wsular/urbanova-aqnet-rpi-node/testing/20161214_rooftest/SOAK2-PM10_004.csv

Instrument Name | DustTrak II
Model Number | 8530
Serial Number | 8530150710
Firmware Version | 3.4
Calibration Date | 2015/02/12
Test Name | SOAK2-PM10_002
Test Start Time | 18:29:04
Test Start Date | 2017/01/05
Test Length [D:H:M] | 3:17:56
Test Interval [M:S] | 1:0
Mass Average [mg/m3] | 0.003
Mass Minimum [mg/m3] | 0.000
Mass Maximum [mg/m3] | 0.009
Mass TWA [mg/m3] | 0.004
Photometric User Cal | 0.38
Flow User Cal | 0.00
Errors
Number of Samples | 5396
Elapsed Time [s] | Mass [mg/m3] | Alarms | Errors
60 | 0.003
120 | 0.003
180 | 0.003
240 | 0.003
300 | 0.003
360 | 0.003
420 | 0.003
480 | 0.003
540 | 0.003
600 | 0.003
660 | 0.003
720 | 0.003
780 | 0.003
840 | 0.003
900 | 0.003
960 | 0.003
1020 | 0.003
1080 | 0.003
1140 | 0.004
1200 | 0.004
1260 | 0.004
1320 | 0.004
1380 | 0.004
1440 | 0.004
1500 | 0.004
1560 | 0.004
1620 | 0.004
1680 | 0.004
1740 | 0.004
1800 | 0.004
1860 | 0.004
1920 | 0.004
1980 | 0.004
2040 | 0.004
2100 | 0.004
2160 | 0.005
2220 | 0.005
2280 | 0.005
2340 | 0.005
2400 | 0.005
2460 | 0.005
2520 | 0.005
2580 | 0.005
2640 | 0.005
2700 | 0.005
2760 | 0.005
2820 | 0.005
2880 | 0.005
2940 | 0.005
3000 | 0.005
3060 | 0.005
3120 | 0.005
3180 | 0.005
3240 | 0.005
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
