wsular/urbanova-aqnet-rpi-node/testing/20161214_rooftest/SOAK2-PM25_001.csv

Instrument Name | DustTrak II
Model Number | 8530
Serial Number | 8530152108
Firmware Version | 3.4
Calibration Date | 2015/05/27
Test Name | SOAK2-PM25_001
Test Start Time | 13:56:33
Test Start Date | 2016/12/15
Test Length [D:H:M] | 7:0:0
Test Interval [M:S] | 0:10
Mass Average [mg/m3] | 0.004
Mass Minimum [mg/m3] | 0.000
Mass Maximum [mg/m3] | 0.035
Mass TWA [mg/m3] | 0.005
Photometric User Cal | 0.38
Flow User Cal | 0.00
Errors
Number of Samples | 60480
Elapsed Time [s] | Mass [mg/m3] | Alarms | Errors
10 | 0.005
20 | 0.004
30 | 0.004
40 | 0.005
50 | 0.004
60 | 0.004
70 | 0.004
80 | 0.005
90 | 0.004
100 | 0.004
110 | 0.004
120 | 0.004
130 | 0.004
140 | 0.004
150 | 0.004
160 | 0.004
170 | 0.003
180 | 0.003
190 | 0.003
200 | 0.004
210 | 0.004
220 | 0.004
230 | 0.004
240 | 0.004
250 | 0.004
260 | 0.004
270 | 0.004
280 | 0.004
290 | 0.004
300 | 0.004
310 | 0.004
320 | 0.004
330 | 0.004
340 | 0.005
350 | 0.004
360 | 0.004
370 | 0.004
380 | 0.004
390 | 0.004
400 | 0.004
410 | 0.004
420 | 0.004
430 | 0.004
440 | 0.004
450 | 0.004
460 | 0.004
470 | 0.004
480 | 0.004
490 | 0.004
500 | 0.004
510 | 0.004
520 | 0.004
530 | 0.004
540 | 0.004
550 | 0.004
560 | 0.004
570 | 0.004
580 | 0.004
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
