wsular/urbanova-aqnet-rpi-node/testing/20161214_rooftest/SOAK2-PM25_002.csv

Instrument Name | DustTrak II
Model Number | 8530
Serial Number | 8530152108
Firmware Version | 3.4
Calibration Date | 2015/05/27
Test Name | SOAK2-PM25_001
Test Start Time | 17:32:23
Test Start Date | 2016/12/22
Test Length [D:H:M] | 5:17:59
Test Interval [M:S] | 0:10
Mass Average [mg/m3] | 0.002
Mass Minimum [mg/m3] | 0.000
Mass Maximum [mg/m3] | 0.015
Mass TWA [mg/m3] | 0.001
Photometric User Cal | 0.38
Flow User Cal | 0.00
Errors
Number of Samples | 49676
Elapsed Time [s] | Mass [mg/m3] | Alarms | Errors
10 | 0.002
20 | 0.002
30 | 0.002
40 | 0.002
50 | 0.002
60 | 0.002
70 | 0.002
80 | 0.002
90 | 0.002
100 | 0.002
110 | 0.002
120 | 0.002
130 | 0.002
140 | 0.002
150 | 0.002
160 | 0.002
170 | 0.002
180 | 0.002
190 | 0.002
200 | 0.002
210 | 0.002
220 | 0.002
230 | 0.002
240 | 0.002
250 | 0.002
260 | 0.002
270 | 0.002
280 | 0.002
290 | 0.002
300 | 0.002
310 | 0.002
320 | 0.002
330 | 0.002
340 | 0.002
350 | 0.002
360 | 0.002
370 | 0.002
380 | 0.002
390 | 0.002
400 | 0.002
410 | 0.002
420 | 0.002
430 | 0.002
440 | 0.002
450 | 0.002
460 | 0.002
470 | 0.002
480 | 0.002
490 | 0.002
500 | 0.002
510 | 0.002
520 | 0.002
530 | 0.002
540 | 0.002
550 | 0.002
560 | 0.002
570 | 0.002
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
